vilhelmprytz/miljomataren/delos/include/Positioning.h

// https://servicepunkten.com/downloads/FGPMMOPA6H_BOB.pdf

#include <Adafruit_GPS.h>
#include <tuple>

// what's the name of the hardware serial port?
#define GPSSerial Serial1

// Connect to the GPS on the hardware port
Adafruit_GPS GPS(&GPSSerial);

// Set GPSECHO to 'false' to turn off echoing the GPS data to the Serial console
// Set to 'true' if you want to debug and listen to the raw GPS sentences
#define GPSECHO false

class Positioning {
public:
  void setup() {
    // 9600 NMEA is the default baud rate for Adafruit MTK GPS's- some use 4800
    GPS.begin(9600);
    // uncomment this line to turn on RMC (recommended minimum) and GGA (fix
    // data) including altitude
    GPS.sendCommand(PMTK_SET_NMEA_OUTPUT_RMCGGA);
    // uncomment this line to turn on only the "minimum recommended" data
    // GPS.sendCommand(PMTK_SET_NMEA_OUTPUT_RMCONLY);
    // For parsing data, we don't suggest using anything but either RMC only or
    // RMC+GGA since the parser doesn't care about other sentences at this time
    // Set the update rate
    GPS.sendCommand(PMTK_SET_NMEA_UPDATE_1HZ); // 1 Hz update rate
    // For the parsing code to work nicely and have time to sort thru the data,
    // and print it out we don't suggest using anything higher than 1 Hz

    // Request updates on antenna status, comment out to keep quiet
    GPS.sendCommand(PGCMD_ANTENNA);

    delay(1000);

    // Ask for firmware version
    GPSSerial.println(PMTK_Q_RELEASE);
  };

  bool loop() {
    // read data from the GPS in the 'main loop'
    char c = GPS.read();
    // if you want to debug, this is a good time to do it!
    if (GPSECHO) {
      if (c) {
        Serial.print(c);
      }
    }
    // if a sentence is received, we can check the checksum, parse it...
    if (GPS.newNMEAreceived()) {
      // a tricky thing here is if we print the NMEA sentence, or data
      // we end up not listening and catching other sentences!
      // so be very wary if using OUTPUT_ALLDATA and trying to print out data
      // this also sets the newNMEAreceived() flag to false
      // Serial.print(GPS.lastNMEA());
      if (!GPS.parse(GPS.lastNMEA())) { // this also sets the newNMEAreceived()
                                        // flag to false
        return false; // we can fail to parse a sentence in which case we should
                      // just wait for another
      }
    }
    return true;
  }

  struct position {
    float lat, lon;
    bool success;
  };

  struct position get_position() {
    Serial.print("\nTime: ");
    if (GPS.hour < 10) {
      Serial.print('0');
    }
    Serial.print(GPS.hour, DEC);
    Serial.print(':');
    if (GPS.minute < 10) {
      Serial.print('0');
    }
    Serial.print(GPS.minute, DEC);
    Serial.print(':');
    if (GPS.seconds < 10) {
      Serial.print('0');
    }
    Serial.print(GPS.seconds, DEC);
    Serial.print('.');
    if (GPS.milliseconds < 10) {
      Serial.print("00");
    } else if (GPS.milliseconds > 9 && GPS.milliseconds < 100) {
      Serial.print("0");
    }
    Serial.println(GPS.milliseconds);
    Serial.print("Fix: ");
    Serial.print((int)GPS.fix);
    Serial.print(" quality: ");
    Serial.println((int)GPS.fixquality);
    if (GPS.fix) {
      Serial.print("Location: ");
      Serial.print(GPS.latitudeDegrees, 6);
      Serial.print(" ");
      Serial.println(GPS.longitudeDegrees, 6);
      Serial.print("Speed (knots): ");
      Serial.println(GPS.speed);
      Serial.print("Angle: ");
      Serial.println(GPS.angle);
      Serial.print("Altitude: ");
      Serial.println(GPS.altitude);
      Serial.print("Satellites: ");
      Serial.println((int)GPS.satellites);

      return position{GPS.latitudeDegrees, GPS.longitudeDegrees, true};
    }

    // no position could be fetched
    return position{0, 0, false};
  };
};
