vilhelmprytz/miljomataren/delos/include/example.config.h

#define SIM_PINNUMBER "";
#define SIM_GPRS_APN "internet";
#define SIM_GPRS_LOGIN "";
#define SIM_GPRS_PASSWORD "";

#define API_HOST "miljomataren.vilhelmprytz.se";
#define API_CAR_ID 1;
#define API_TOKEN "";
